picafe/piLinkE/images/X2_B9miYtfZcf.png

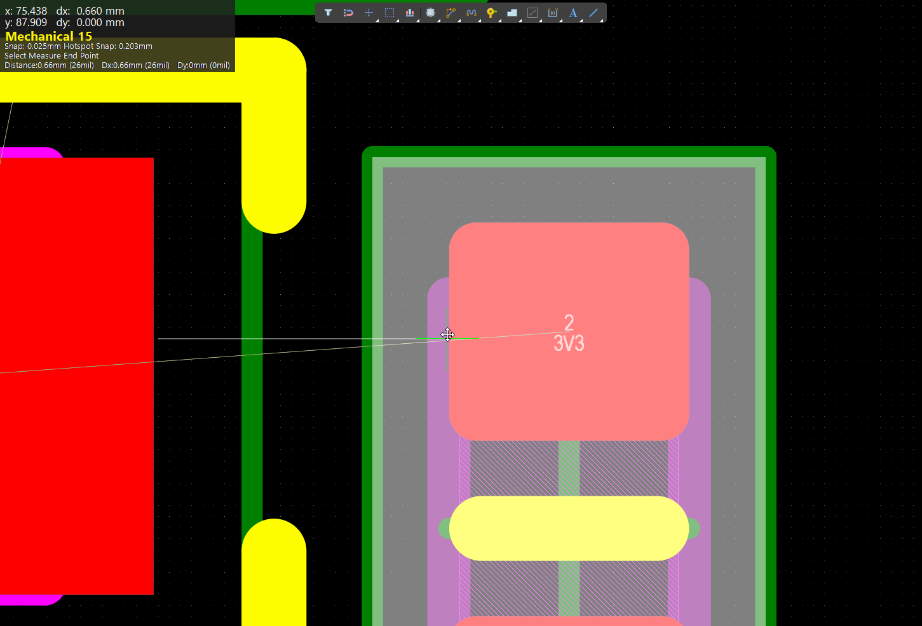
images/X2_B9miYtfZcf.png
