picafe/piLinkE/images/X2_zpv3dikva5.png

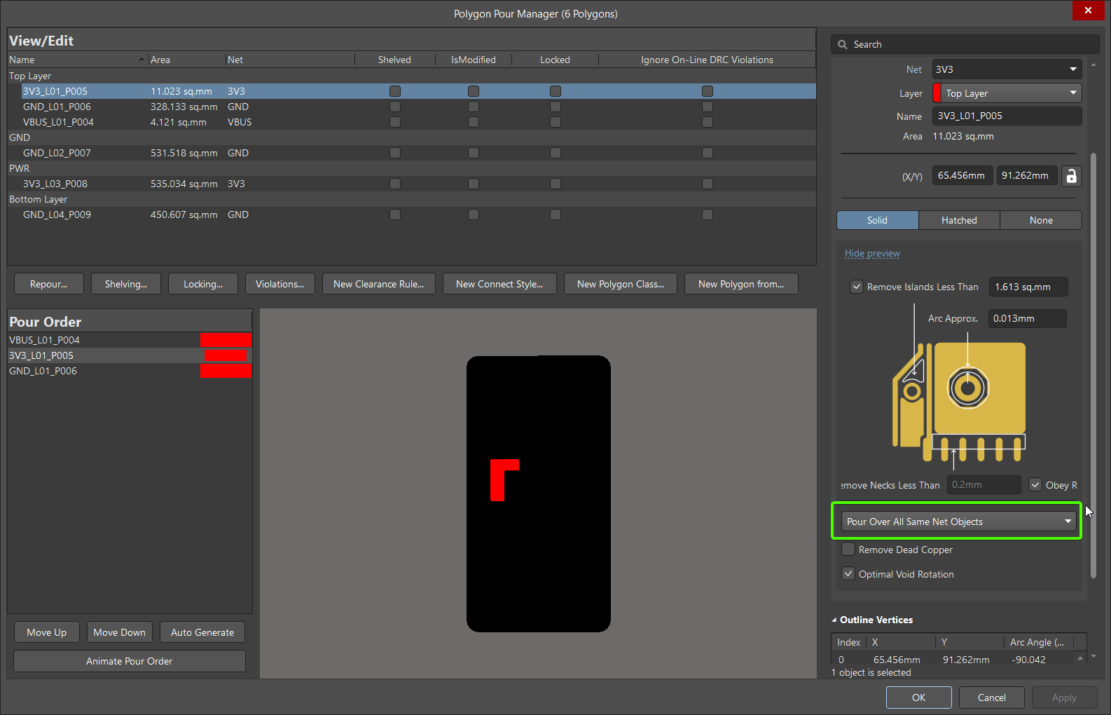
images/X2_zpv3dikva5.png
